pansapiens/blue-peaks/firmware/peaks2/modulations/lfo.cc

// Copyright 2013 Emilie Gillet, 2015 Tim Churches
//
// Author: Emilie Gillet (emilie.o.gillet@gmail.com)
// Modifications: Tim Churches (tim.churches@gmail.com)
// Modifications may be determined by examining the differences between the last commit
// by Emilie Gillet (pichenettes) and the HEAD commit at
// https://github.com/timchurches/Mutated-Mutables/tree/master/peaks
//
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
// See http://creativecommons.org/licenses/MIT/ for more information.
//
// -----------------------------------------------------------------------------
//
// LFO.

#include "peaks2/modulations/lfo.h"

#include <cstdio>

#include "stmlib/utils/dsp.h"
#include "stmlib/utils/random.h"

#include "peaks2/resources.h"

namespace peaks {

const uint16_t kSlopeBits = 12;
const uint32_t kSyncCounterMaxTime = 8 * 48000;

using namespace stmlib;

void Lfo::Init() {
  rate_ = 0;
  shape_ = LFO_SHAPE_SQUARE;
  parameter_ = 0;
  reset_phase_ = 0;
  sync_ = false;
  previous_parameter_ = 32767;
  sync_counter_ = kSyncCounterMaxTime;
  level_ = 32767;
  pattern_predictor_.Init();
}

const int16_t presets[7][2] = {
  { LFO_SHAPE_SINE, 0 },
  { LFO_SHAPE_TRIANGLE, 0 },
  { LFO_SHAPE_TRIANGLE, 32767 },
  { LFO_SHAPE_SQUARE, 0 },
  { LFO_SHAPE_STEPS, 0 },
  { LFO_SHAPE_NOISE, -32767 },
  { LFO_SHAPE_NOISE, 32767 },
};

void Lfo::set_shape_parameter_preset(uint16_t value) {
  value = (value >> 8) * 7 >> 8;
  set_shape(static_cast<LfoShape>(presets[value][0]));
  set_parameter(presets[value][1]);
}

void Lfo::Process(const GateFlags* gate_flags, int16_t* out, size_t size) {
  if (!sync_) {
    int32_t a = lut_lfo_increments[rate_ >> 8];
    int32_t b = lut_lfo_increments[(rate_ >> 8) + 1];
    phase_increment_ = a + (((b - a) >> 1) * (rate_ & 0xff) >> 7);
  }
  while (size--) {
    ++sync_counter_;
    GateFlags gate_flag = *gate_flags++;
    if (gate_flag & GATE_FLAG_RISING) {
      bool reset_phase = true;
      if (sync_) {
        if (sync_counter_ < kSyncCounterMaxTime) {
          uint32_t period = 0;
          if (gate_flag & GATE_FLAG_FROM_BUTTON) {
            period = sync_counter_;
          } else if (sync_counter_ < 1920) {
            period = (3 * period_ + sync_counter_) >> 2;
            reset_phase = false;
          } else {
            period = pattern_predictor_.Predict(sync_counter_);
          }
          if (period != period_) {
            period_ = period;
            phase_increment_ = 0xffffffff / period_;
          }
        }
        sync_counter_ = 0;
      }
      if (reset_phase) {
        phase_ = reset_phase_;
      }
    }
    phase_ += phase_increment_;
    int32_t sample = (this->*compute_sample_fn_table_[shape_])();
    *out++ = sample * level_ >> 15;
  }
}

int16_t Lfo::ComputeSampleSine() {
  uint32_t phase = phase_;
  int16_t sine = Interpolate1022(wav_sine, phase);
  int16_t sample;
  if (parameter_ > 0) {
    int32_t wf_balance = parameter_;
    int32_t wf_gain = 2048 + \
        (static_cast<int32_t>(parameter_) * (65535 - 2048) >> 15);
    int32_t original = sine;
    int32_t folded = Interpolate1022(
        wav_fold_sine, original * wf_gain + (1UL << 31));
    sample = original + ((folded - original) * wf_balance >> 15);
  } else {
    int32_t wf_balance = -parameter_;
    int32_t original = sine;
    phase += 1UL << 30;
    int32_t tri = phase < (1UL << 31) ? phase << 1 : ~(phase << 1);
    int32_t folded = Interpolate1022(wav_fold_power, tri);
    sample = original + ((folded - original) * wf_balance >> 15);
  }
  return sample;
}

int16_t Lfo::ComputeSampleTriangle() {
  if (parameter_ != previous_parameter_) {
    uint16_t slope_offset = parameter_ + 32768;
    if (slope_offset <= 1) {
      decay_factor_ = 32768 << kSlopeBits;
      attack_factor_ = 1 << (kSlopeBits - 1);
    } else {
      decay_factor_ = (32768 << kSlopeBits) / slope_offset;
      attack_factor_ = (32768 << kSlopeBits) / (65536 - slope_offset);
    }
    end_of_attack_ = (static_cast<uint32_t>(slope_offset) << 16);
    previous_parameter_ = parameter_;
  }

  uint32_t phase = phase_;
  uint32_t skewed_phase = phase;
  if (phase < end_of_attack_) {
    skewed_phase = (phase >> kSlopeBits) * decay_factor_;
  } else {
    skewed_phase = ((phase - end_of_attack_) >> kSlopeBits) * attack_factor_;
    skewed_phase += 1L << 31;
  }
  return skewed_phase < 1UL << 31
      ? -32768 + (skewed_phase >> 15)
      :  32767 - (skewed_phase >> 15);
}

int16_t Lfo::ComputeSampleSquare() {
  uint32_t threshold = static_cast<uint32_t>(parameter_ + 32768) << 16;
  if (threshold < (phase_increment_ << 1)) {
    threshold = phase_increment_ << 1;
  } else if (~threshold < (phase_increment_ << 1)) {
    threshold = ~(phase_increment_ << 1);
  }
  return phase_ < threshold ? 32767 : -32767;
}

int16_t Lfo::ComputeSampleSteps() {
  uint16_t quantization_levels = 2 + (((parameter_ + 32768) * 15) >> 16);
  uint16_t scale = 65535 / (quantization_levels - 1);
  uint32_t phase = phase_;
  uint32_t tri_phase = phase;
  uint32_t tri = tri_phase < (1UL << 31) ? tri_phase << 1 : ~(tri_phase << 1);
  return ((tri >> 16) * quantization_levels >> 16) * scale - 32768;
}

int16_t Lfo::ComputeSampleNoise() {
  uint32_t phase = phase_;
  if (phase < phase_increment_) {
    value_ = next_value_;
    next_value_ = Random::GetSample();
  }
  int16_t sample;
  int32_t linear_interpolation = value_ + \
      ((next_value_ - value_) * static_cast<int32_t>(phase >> 17) >> 15);
  if (parameter_ < 0) {
    int32_t balance = parameter_ + 32767;
    sample = value_ + ((linear_interpolation - value_) * balance >> 15);
  } else {
    int16_t raised_cosine = Interpolate824(lut_raised_cosine, phase) >> 1;
    int32_t smooth_interpolation = value_ + \
        ((next_value_ - value_) * raised_cosine >> 15);
    sample = linear_interpolation + \
        ((smooth_interpolation - linear_interpolation) * parameter_ >> 15);
  }
  return sample;
}

/* static */
Lfo::ComputeSampleFn Lfo::compute_sample_fn_table_[] = {
  &Lfo::ComputeSampleSine,
  &Lfo::ComputeSampleTriangle,
  &Lfo::ComputeSampleSquare,
  &Lfo::ComputeSampleSteps,
  &Lfo::ComputeSampleNoise
};

// Repeat for internally frequency-modulated LFO

void FmLfo::Init() {
  rate_ = 0;
  shape_ = LFO_SHAPE_SQUARE;
  parameter_ = 0;
  reset_phase_ = 0;
  previous_parameter_ = 32767;
  level_ = 32767;
  fm_rate_ = 0;
  fm_parameter_ = 0;
  fm_reset_phase_ = 0;
  fm_delta_ = 0 ;

}

void FmLfo::set_shape_parameter_preset(uint16_t value) {
  value = (value >> 8) * 7 >> 8;
  set_shape(static_cast<LfoShape>(presets[value][0]));
  set_parameter(presets[value][1]);
}

void FmLfo::Process(const GateFlags* gate_flags, int16_t* out, size_t size) {
  while (size--) {
    // internal FM oscillator first
    int32_t fm_a = lut_lfo_increments[fm_rate_ >> 8];
    int32_t fm_b = lut_lfo_increments[(fm_rate_ >> 8) + 1];
    fm_phase_increment_ = fm_a + (((fm_b - fm_a) >> 1) * (fm_rate_ & 0xff) >> 7);

    GateFlags gate_flag = *gate_flags++;
    if (gate_flag & GATE_FLAG_RISING) {
      bool fm_reset_phase = true;
      if (fm_reset_phase) {
        fm_phase_ = fm_reset_phase_;
      }
    }

    fm_phase_ += fm_phase_increment_;
    int32_t fm_sample = FmLfo::ComputeModulation();
    fm_delta_ = (fm_sample * fm_depth_) >> 18;
    // now actual LFO
    uint32_t unclipped_modulated_rate = rate_ + fm_delta_;
    if (unclipped_modulated_rate > 65535) {
      unclipped_modulated_rate = 65335 ;
    } else if (unclipped_modulated_rate <0) {
      unclipped_modulated_rate = 0 ;
    }
    uint16_t modulated_rate = static_cast<uint16_t>(unclipped_modulated_rate) ;
    int32_t a = lut_lfo_increments[modulated_rate >> 8];
    int32_t b = lut_lfo_increments[(modulated_rate >> 8) + 1];
    phase_increment_ = a + (((b - a) >> 1) * (modulated_rate & 0xff) >> 7);

    if (gate_flag & GATE_FLAG_RISING) {
      bool reset_phase = true;
      if (reset_phase) {
        phase_ = reset_phase_;
      }
    }
    phase_ += phase_increment_;
    int32_t sample = (this->*compute_sample_fn_table_[shape_])();
    *out++ = sample * level_ >> 15;
  }
}

int16_t FmLfo::ComputeSampleSine() {
  uint32_t phase = phase_;
  int16_t sine = Interpolate1022(wav_sine, phase);
  int16_t sample;
  if (parameter_ > 0) {
    int32_t wf_balance = parameter_;
    int32_t wf_gain = 2048 + \
        (static_cast<int32_t>(parameter_) * (65535 - 2048) >> 15);
    int32_t original = sine;
    int32_t folded = Interpolate1022(
        wav_fold_sine, original * wf_gain + (1UL << 31));
    sample = original + ((folded - original) * wf_balance >> 15);
  } else {
    int32_t wf_balance = -parameter_;
    int32_t original = sine;
    phase += 1UL << 30;
    int32_t tri = phase < (1UL << 31) ? phase << 1 : ~(phase << 1);
    int32_t folded = Interpolate1022(wav_fold_power, tri);
    sample = original + ((folded - original) * wf_balance >> 15);
  }
  return sample;
}

int16_t FmLfo::ComputeModulation() {
  uint32_t phase = fm_phase_;
  int16_t sine = Interpolate1022(wav_sine, phase);
  int16_t sample;
  if (!random_mod_) {
    int32_t wf_balance = fm_parameter_;
    int32_t wf_gain = 2048 + \
          (static_cast<int32_t>(fm_parameter_) * (65535 - 2048) >> 15);
    int32_t original = sine;
    int32_t folded = Interpolate1022(
          wav_fold_sine, original * wf_gain + (1UL << 31));
    sample = original + ((folded - original) * wf_balance >> 15);
  } else {
    if (phase < fm_phase_increment_) {
      fm_value_ = fm_next_value_;
      fm_next_value_ = Random::GetSample();
    }
    int32_t linear_interpolation = fm_value_ + \
        ((fm_next_value_ - fm_value_) * static_cast<int32_t>(phase >> 17) >> 15);
    int16_t raised_cosine = Interpolate824(lut_raised_cosine, phase) >> 1;
    int32_t smooth_interpolation = fm_value_ + \
          ((next_value_ - fm_value_) * raised_cosine >> 15);
    sample = linear_interpolation + \
          ((smooth_interpolation - linear_interpolation) * fm_parameter_ >> 15);
  }
  return sample;
}

int16_t FmLfo::ComputeSampleTriangle() {
  if (parameter_ != previous_parameter_) {
    uint16_t slope_offset = parameter_ + 32768;
    if (slope_offset <= 1) {
      decay_factor_ = 32768 << kSlopeBits;
      attack_factor_ = 1 << (kSlopeBits - 1);
    } else {
      decay_factor_ = (32768 << kSlopeBits) / slope_offset;
      attack_factor_ = (32768 << kSlopeBits) / (65536 - slope_offset);
    }
    end_of_attack_ = (static_cast<uint32_t>(slope_offset) << 16);
    previous_parameter_ = parameter_;
  }

  uint32_t phase = phase_;
  uint32_t skewed_phase = phase;
  if (phase < end_of_attack_) {
    skewed_phase = (phase >> kSlopeBits) * decay_factor_;
  } else {
    skewed_phase = ((phase - end_of_attack_) >> kSlopeBits) * attack_factor_;
    skewed_phase += 1L << 31;
  }
  return skewed_phase < 1UL << 31
      ? -32768 + (skewed_phase >> 15)
      :  32767 - (skewed_phase >> 15);
}

int16_t FmLfo::ComputeSampleSquare() {
  uint32_t threshold = static_cast<uint32_t>(parameter_ + 32768) << 16;
  if (threshold < (phase_increment_ << 1)) {
    threshold = phase_increment_ << 1;
  } else if (~threshold < (phase_increment_ << 1)) {
    threshold = ~(phase_increment_ << 1);
  }
  return phase_ < threshold ? 32767 : -32767;
}

int16_t FmLfo::ComputeSampleSteps() {
  uint16_t quantization_levels = 2 + (((parameter_ + 32768) * 15) >> 16);
  uint16_t scale = 65535 / (quantization_levels - 1);
  uint32_t phase = phase_;
  uint32_t tri_phase = phase;
  uint32_t tri = tri_phase < (1UL << 31) ? tri_phase << 1 : ~(tri_phase << 1);
  return ((tri >> 16) * quantization_levels >> 16) * scale - 32768;
}

int16_t FmLfo::ComputeSampleNoise() {
  uint32_t phase = phase_;
  if (phase < phase_increment_) {
    value_ = next_value_;
    next_value_ = Random::GetSample();
  }
  int16_t sample;
  int32_t linear_interpolation = value_ + \
      ((next_value_ - value_) * static_cast<int32_t>(phase >> 17) >> 15);
  if (parameter_ <= 0) {
    int32_t balance = parameter_ + 32767;
    sample = value_ + ((linear_interpolation - value_) * balance >> 15);
  } else {
    int16_t raised_cosine = Interpolate824(lut_raised_cosine, phase) >> 1;
    int32_t smooth_interpolation = value_ + \
        ((next_value_ - value_) * raised_cosine >> 15);
    sample = linear_interpolation + \
        ((smooth_interpolation - linear_interpolation) * parameter_ >> 15);
  }
  return sample;
}

/* static */
FmLfo::ComputeSampleFn FmLfo::compute_sample_fn_table_[] = {
  &FmLfo::ComputeSampleSine,
  &FmLfo::ComputeSampleTriangle,
  &FmLfo::ComputeSampleSquare,
  &FmLfo::ComputeSampleSteps,
  &FmLfo::ComputeSampleNoise
};

////////////////////////////////////////////////
// Repeat for internally waveshape-modulated LFO

void WsmLfo::Init() {
  rate_ = 0;
  shape_ = WSMLFO_SHAPE_SQUARE;
  parameter_ = 0;
  reset_phase_ = 0;
  previous_parameter_ = 32767;
  level_ = 32767;
  wsm_rate_ = 0;
  wsm_parameter_ = 0;
  wsm_reset_phase_ = 0;
  wsm_delta_ = 0 ;
}

const int16_t wsmlfo_presets[7][2] = {
  { WSMLFO_SHAPE_FOLDED_SINE, 0 },
  { WSMLFO_SHAPE_FOLDED_POWER_SINE, 0 },
  { WSMLFO_SHAPE_OVERDRIVEN_SINE, 0 },
  { WSMLFO_SHAPE_TRIANGLE, 0 },
  { WSMLFO_SHAPE_TRIANGLE, 32767 },
  { WSMLFO_SHAPE_SQUARE, 0 },
  { WSMLFO_SHAPE_NOISE, -32767 },
  // { WSMLFO_SHAPE_NOISE, 32767 },
} ;

void WsmLfo::set_shape_parameter_preset(uint16_t value) {
  value = (value >> 8) * 7 >> 8;
  set_shape(static_cast<WsmLfoShape>(presets[value][0]));
  set_parameter(presets[value][1]);
}

void WsmLfo::Process(const GateFlags* gate_flags, int16_t* out, size_t size) {
  while (size--) {
    // internal waveshape modulation oscillator first
    int32_t wsm_a = lut_lfo_increments[wsm_rate_ >> 8];
    int32_t wsm_b = lut_lfo_increments[(wsm_rate_ >> 8) + 1];
    wsm_phase_increment_ = wsm_a + (((wsm_b - wsm_a) >> 1) * (wsm_rate_ & 0xff) >> 7);
    GateFlags gate_flag = *gate_flags++;
    if (gate_flag & GATE_FLAG_RISING) {
      bool wsm_reset_phase = true;
      if (wsm_reset_phase) {
        wsm_phase_ = wsm_reset_phase_;
      }
    }
    wsm_phase_ += wsm_phase_increment_;
    int32_t wsm_sample = WsmLfo::ComputeModulation();
    wsm_delta_ = (wsm_sample * wsm_depth_) >> 16;
    parameter_ = wsm_delta_ ;
    // now actual LFO
    int32_t a = lut_lfo_increments[rate_ >> 8];
    int32_t b = lut_lfo_increments[(rate_ >> 8) + 1];
    phase_increment_ = a + (((b - a) >> 1) * (rate_ & 0xff) >> 7);
    if (gate_flag & GATE_FLAG_RISING) {
      bool reset_phase = true;
      if (reset_phase) {
        phase_ = reset_phase_;
      }
    }
    phase_ += phase_increment_;
    int32_t sample = (this->*compute_sample_fn_table_[shape_])();
    *out++ = sample;
  }
}

int16_t WsmLfo::ComputeSampleFoldedSine() {
  uint32_t phase = phase_;
  int16_t sine = Interpolate1022(wav_sine, phase);
  int16_t sample;
  int32_t wf_balance = (parameter_ + 32767) >> 1;
  int32_t wf_gain = 2048 + \
        (static_cast<int32_t>(parameter_) * (65535 - 2048) >> 15);
  int32_t original = sine;
  int32_t folded = Interpolate1022(
        wav_fold_sine, original * wf_gain + (1UL << 31));
  sample = original + ((folded - original) * wf_balance >> 15);
  return sample;
}

int16_t WsmLfo::ComputeSampleFoldedPowerSine() {
  uint32_t phase = phase_;
  int16_t sine = Interpolate1022(wav_sine, phase);
  int16_t sample;
  int32_t wf_balance = (parameter_ + 32767) >> 1;
  int32_t original = sine;
  phase += 1UL << 30;
  int32_t tri = phase < (1UL << 31) ? phase << 1 : ~(phase << 1);
  int32_t folded = Interpolate1022(wav_fold_power, tri);
  sample = original + ((folded - original) * wf_balance >> 15);
  return sample ;
}

int16_t WsmLfo::ComputeSampleOverdrivenSine() {
  uint32_t phase = phase_;
  int16_t sine = Interpolate1022(wav_sine, phase);
  int16_t sample;
  int32_t wf_balance = (parameter_ + 32767) >> 1;
  int32_t wf_gain = 2048 + \
        (static_cast<int32_t>(parameter_) * (65535 - 2048) >> 15);
  int32_t original = sine;
  int32_t folded = Interpolate1022(
        wav_overdrive, original * wf_gain + (1UL << 31));
  sample = original + ((folded - original) * wf_balance >> 15);
  return sample;
}

int16_t WsmLfo::ComputeModulation() {
  uint32_t phase = wsm_phase_;
  int16_t sample;
  if (!random_mod_) {
    int16_t sine = Interpolate1022(wav_sine, phase);
    int32_t wf_balance = wsm_parameter_;
    int32_t wf_gain = 2048 + \
        (static_cast<int32_t>(wsm_parameter_) * (65535 - 2048) >> 15);
    int32_t original = sine;
    int32_t folded = Interpolate1022(
        wav_fold_sine, original * wf_gain + (1UL << 31));
    sample = original + ((folded - original) * wf_balance >> 15);
  } else {
    if (phase < wsm_phase_increment_) {
      wsm_value_ = wsm_next_value_;
      wsm_next_value_ = Random::GetSample();
    }
    int32_t linear_interpolation = wsm_value_ + \
        ((wsm_next_value_ - wsm_value_) * static_cast<int32_t>(phase >> 17) >> 15);
    int16_t raised_cosine = Interpolate824(lut_raised_cosine, phase) >> 1;
    int32_t smooth_interpolation = wsm_value_ + \
          ((wsm_next_value_ - wsm_value_) * raised_cosine >> 15);
    sample = linear_interpolation + \
          ((smooth_interpolation - linear_interpolation) * wsm_parameter_ >> 15);
  }
  return sample;
}

int16_t WsmLfo::ComputeSampleTriangle() {
  if (parameter_ != previous_parameter_) {
    uint16_t slope_offset = parameter_ + 32768;
    if (slope_offset <= 1) {
      decay_factor_ = 32768 << kSlopeBits;
      attack_factor_ = 1 << (kSlopeBits - 1);
    } else {
      decay_factor_ = (32768 << kSlopeBits) / slope_offset;
      attack_factor_ = (32768 << kSlopeBits) / (65536 - slope_offset);
    }
    end_of_attack_ = (static_cast<uint32_t>(slope_offset) << 16);
    previous_parameter_ = parameter_;
  }

  uint32_t phase = phase_;
  uint32_t skewed_phase = phase;
  if (phase < end_of_attack_) {
    skewed_phase = (phase >> kSlopeBits) * decay_factor_;
  } else {
    skewed_phase = ((phase - end_of_attack_) >> kSlopeBits) * attack_factor_;
    skewed_phase += 1L << 31;
  }
  return skewed_phase < 1UL << 31
      ? -32768 + (skewed_phase >> 15)
      :  32767 - (skewed_phase >> 15);
}

int16_t WsmLfo::ComputeSampleSquare() {
  uint32_t threshold = static_cast<uint32_t>(parameter_ + 32768) << 16;
  if (threshold < (phase_increment_ << 1)) {
    threshold = phase_increment_ << 1;
  } else if (~threshold < (phase_increment_ << 1)) {
    threshold = ~(phase_increment_ << 1);
  }
  return phase_ < threshold ? 32767 : -32767;
}

int16_t WsmLfo::ComputeSampleNoise() {
  uint32_t phase = phase_;
  if (phase < phase_increment_) {
    value_ = next_value_;
    next_value_ = Random::GetSample();
  }
  int16_t sample;
  int32_t linear_interpolation = value_ + \
      ((next_value_ - value_) * static_cast<int32_t>(phase >> 17) >> 15);
  if (parameter_ <= 0) {
    int32_t balance = parameter_ + 32767;
    sample = value_ + ((linear_interpolation - value_) * balance >> 15);
  } else {
    int16_t raised_cosine = Interpolate824(lut_raised_cosine, phase) >> 1;
    int32_t smooth_interpolation = value_ + \
        ((next_value_ - value_) * raised_cosine >> 15);
    sample = linear_interpolation + \
        ((smooth_interpolation - linear_interpolation) * parameter_ >> 15);
  }
  return sample;
}

/* static */
WsmLfo::ComputeSampleFn WsmLfo::compute_sample_fn_table_[] = {
  &WsmLfo::ComputeSampleFoldedSine,
  &WsmLfo::ComputeSampleFoldedPowerSine,
  &WsmLfo::ComputeSampleOverdrivenSine,
  &WsmLfo::ComputeSampleTriangle,
  &WsmLfo::ComputeSampleSquare,
  &WsmLfo::ComputeSampleNoise
};

///////////////////////////////////////////
// Repeat for audio-frequency PLL oscillator

void Plo::Init() {
  rate_ = 0;
  shape_ = WSMLFO_SHAPE_SQUARE;
  parameter_ = 0;
  // reset_phase_ = 0;
  sync_ = true;
  previous_parameter_ = 32767;
  level_ = 32767;
  wsm_rate_ = 0;
  wsm_parameter_ = 0;
  // wsm_reset_phase_ = 0;
  // wsm_delta_ = 0 ;

  sync_counter_ = kSyncCounterMaxTime;
  pattern_predictor_.Init();

  pitch_multiplier_ = 0;
}

void Plo::set_shape_parameter_preset(uint16_t value) {
  value = (value >> 8) * 7 >> 8;
  set_shape(static_cast<WsmLfoShape>(presets[value][0]));
  set_parameter(presets[value][1]);
}

void Plo::set_pitch_coefficient(uint16_t value) {
  pitch_multiplier_ = static_cast<int8_t>(static_cast<int16_t>(-32767 + value) >> 13);
}

void Plo::Process(const GateFlags* gate_flags, int16_t* out, size_t size) {
  while (size--) {
    GateFlags gate_flag = *gate_flags++;

    // internal waveshape modulation oscillator first
    if (wsm_depth_) {
      int32_t wsm_a = lut_lfo_increments[wsm_rate_ >> 8];
      int32_t wsm_b = lut_lfo_increments[(wsm_rate_ >> 8) + 1];
      wsm_phase_increment_ = wsm_a + (((wsm_b - wsm_a) >> 1) * (wsm_rate_ & 0xff) >> 7);
      wsm_phase_ += wsm_phase_increment_;
      int32_t wsm_sample = Plo::ComputeModulationSine();
      parameter_ = (wsm_sample * wsm_depth_) >> 16;
    }

    ++sync_counter_;
    if (gate_flag & GATE_FLAG_RISING) {
        if (sync_counter_ < kSyncCounterMaxTime) {
          uint32_t period = 0;
          if (sync_counter_ < 1920) {
            period = (3 * period_ + sync_counter_) >> 2;
          } else {
            period = pattern_predictor_.Predict(sync_counter_);
          }
          if (period != period_) {
            period_ = period;
            phase_increment_ = 0xffffffff / period;
            phase_increment_ = pitch_multiplier_ < 0 ?
                                phase_increment_ >> -pitch_multiplier_ :
                                phase_increment_ << pitch_multiplier_ ;
          }
        }
        sync_counter_ = 0;
    }
    phase_ += phase_increment_;
    // int32_t sample = (this->*compute_sample_fn_table_[shape_])();
    // output_buffer->Overwrite(sample);
    *out++ = (this->*compute_sample_fn_table_[shape_])();
  }
}

int16_t Plo::ComputeSampleFoldedSine() {
  uint32_t phase = phase_;
  int16_t sine = Interpolate1022(wav_sine, phase);
  int16_t sample;
  int32_t wf_balance = (parameter_ + 32767) >> 1;
  int32_t wf_gain = 2048 + \
        (static_cast<int32_t>(parameter_) * (65535 - 2048) >> 15);
  int32_t original = sine;
  int32_t folded = Interpolate1022(
        wav_fold_sine, original * wf_gain + (1UL << 31));
  sample = original + ((folded - original) * wf_balance >> 15);
  return sample;
}

int16_t Plo::ComputeSampleFoldedPowerSine() {
  uint32_t phase = phase_;
  int16_t sine = Interpolate1022(wav_sine, phase);
  int16_t sample;
  int32_t wf_balance = (parameter_ + 32767) >> 1;
  int32_t original = sine;
  phase += 1UL << 30;
  int32_t tri = phase < (1UL << 31) ? phase << 1 : ~(phase << 1);
  int32_t folded = Interpolate1022(wav_fold_power, tri);
  sample = original + ((folded - original) * wf_balance >> 15);
  return sample ;
}

int16_t Plo::ComputeSampleOverdrivenSine() {
  uint32_t phase = phase_;
  int16_t sine = Interpolate1022(wav_sine, phase);
  int16_t sample;
  int32_t wf_balance = (parameter_ + 32767) >> 1;
  int32_t wf_gain = 2048 + \
        (static_cast<int32_t>(parameter_) * (65535 - 2048) >> 15);
  int32_t original = sine;
  int32_t folded = Interpolate1022(
        wav_overdrive, original * wf_gain + (1UL << 31));
  sample = original + ((folded - original) * wf_balance >> 15);
  return sample;
}

int16_t Plo::ComputeModulationSine() {
  uint32_t phase = wsm_phase_;
  int16_t sine = Interpolate1022(wav_sine, phase);
  return sine ;
}

int16_t Plo::ComputeSampleTriangle() {
  if (parameter_ != previous_parameter_) {
    uint16_t slope_offset = parameter_ + 32768;
    if (slope_offset <= 1) {
      decay_factor_ = 32768 << kSlopeBits;
      attack_factor_ = 1 << (kSlopeBits - 1);
    } else {
      decay_factor_ = (32768 << kSlopeBits) / slope_offset;
      attack_factor_ = (32768 << kSlopeBits) / (65536 - slope_offset);
    }
    end_of_attack_ = (static_cast<uint32_t>(slope_offset) << 16);
    previous_parameter_ = parameter_;
  }

  uint32_t phase = phase_;
  uint32_t skewed_phase = phase;
  if (phase < end_of_attack_) {
    skewed_phase = (phase >> kSlopeBits) * decay_factor_;
  } else {
    skewed_phase = ((phase - end_of_attack_) >> kSlopeBits) * attack_factor_;
    skewed_phase += 1L << 31;
  }
  return skewed_phase < 1UL << 31
      ? -32768 + (skewed_phase >> 15)
      :  32767 - (skewed_phase >> 15);
}

int16_t Plo::ComputeSampleSquare() {
  uint32_t threshold = static_cast<uint32_t>(parameter_ + 32768) << 16;
  if (threshold < (phase_increment_ << 1)) {
    threshold = phase_increment_ << 1;
  } else if (~threshold < (phase_increment_ << 1)) {
    threshold = ~(phase_increment_ << 1);
  }
  return phase_ < threshold ? 32767 : -32767;
}

int16_t Plo::ComputeSampleNoise() {
  uint32_t phase = phase_;
  if (phase < phase_increment_) {
    value_ = next_value_;
    next_value_ = Random::GetSample();
  }
  int16_t sample;
  int32_t linear_interpolation = value_ + \
      ((next_value_ - value_) * static_cast<int32_t>(phase >> 17) >> 15);
  if (parameter_ < 0) {
    int32_t balance = parameter_ + 32767;
    sample = value_ + ((linear_interpolation - value_) * balance >> 15);
  } else {
    int16_t raised_cosine = Interpolate824(lut_raised_cosine, phase) >> 1;
    int32_t smooth_interpolation = value_ + \
        ((next_value_ - value_) * raised_cosine >> 15);
    sample = linear_interpolation + \
        ((smooth_interpolation - linear_interpolation) * parameter_ >> 15);
  }
  return sample;
}

/* static */
Plo::ComputeSampleFn Plo::compute_sample_fn_table_[] = {
  &Plo::ComputeSampleFoldedSine,
  &Plo::ComputeSampleFoldedPowerSine,
  &Plo::ComputeSampleOverdrivenSine,
  &Plo::ComputeSampleTriangle,
  &Plo::ComputeSampleSquare,
  &Plo::ComputeSampleNoise
};

}  // namespace peaks
