pansapiens/blue-peaks/firmware/peaks2/modulations/multistage_envelope.h

// Copyright 2013 Emilie Gillet, 2015 Tim Churches
//
// Author: Emilie Gillet (emilie.o.gillet@gmail.com)
// Modifications: Tim Churches (tim.churches@gmail.com)
// Modifications may be determined by examining the differences between the last commit
// by Emilie Gillet (pichenettes) and the HEAD commit at
// https://github.com/timchurches/Mutated-Mutables/tree/master/peaks
//
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
// See http://creativecommons.org/licenses/MIT/ for more information.
//
// -----------------------------------------------------------------------------
//
// Multistage envelope.

#ifndef PEAKS_MODULATIONS_MULTISTAGE_ENVELOPE_H_
#define PEAKS_MODULATIONS_MULTISTAGE_ENVELOPE_H_

#include "stmlib/stmlib.h"
#include "stmlib/utils/ring_buffer.h"

#include "peaks2/gate_processor.h"

namespace peaks {

enum EnvelopeShape {
  ENV_SHAPE_LINEAR,
  ENV_SHAPE_EXPONENTIAL,
  ENV_SHAPE_QUARTIC
};

const uint16_t kMaxNumSegments = 8;

class MultistageEnvelope {
 public:
  MultistageEnvelope() { }
  ~MultistageEnvelope() { }

  void Init();
  void Process(const GateFlags* gate_flags, int16_t* out, size_t size);

  void Configure(uint16_t* parameter, ControlMode control_mode) {
    if (control_mode == CONTROL_MODE_HALF) {
      set_ad(parameter[0], parameter[1]);
    } else {
      set_adsr(parameter[0], parameter[1], parameter[2] >> 1, parameter[3]);
    }
    if (segment_ > num_segments_) {
      segment_ = 0;
      phase_ = 0;
      value_ = 0;
    }
  }

  inline void set_time(uint16_t segment, uint16_t time) {
    time_[segment] = time;
  }

  inline void set_level(uint16_t segment, int16_t level) {
    level_[segment] = level;
  }

  inline void set_num_segments(uint16_t num_segments) {
    num_segments_ = num_segments;
  }

  inline void set_sustain_point(uint16_t sustain_point) {
    sustain_point_ = sustain_point;
  }

  inline void set_adsr(
      uint16_t attack,
      uint16_t decay,
      uint16_t sustain,
      uint16_t release) {
    num_segments_ = 3;
    sustain_point_ = 2;

    level_[0] = 0;
    level_[1] = 32767;
    level_[2] = sustain;
    level_[3] = 0;

    time_[0] = attack;
    time_[1] = decay;
    time_[2] = release;

    shape_[0] = ENV_SHAPE_QUARTIC;
    shape_[1] = ENV_SHAPE_EXPONENTIAL;
    shape_[2] = ENV_SHAPE_EXPONENTIAL;

    loop_start_ = loop_end_ = 0;
  }

  inline void set_ad(uint16_t attack, uint16_t decay) {
    num_segments_ = 2;
    sustain_point_ = 0;

    level_[0] = 0;
    level_[1] = 32767;
    level_[2] = 0;

    time_[0] = attack;
    time_[1] = decay;

    shape_[0] = ENV_SHAPE_QUARTIC;
    shape_[1] = ENV_SHAPE_EXPONENTIAL;

    loop_start_ = loop_end_ = 0;
  }

  inline void set_hard_reset(bool hard_reset) {
    hard_reset_ = hard_reset;
  }

 private:
  int16_t level_[kMaxNumSegments];
  uint16_t time_[kMaxNumSegments];
  EnvelopeShape shape_[kMaxNumSegments];

  int16_t segment_;
  int16_t start_value_;
  int16_t value_;

  uint32_t phase_;
  uint32_t phase_increment_;

  uint16_t num_segments_;
  uint16_t sustain_point_;
  uint16_t loop_start_;
  uint16_t loop_end_;

  bool hard_reset_;

  DISALLOW_COPY_AND_ASSIGN(MultistageEnvelope);
};

// Just copy the class and adjust it rather than trying to subclass it...
class DualAttackEnvelope {
 public:
  DualAttackEnvelope() { }
  ~DualAttackEnvelope() { }

  void Init();
  void Process(const GateFlags* gate_flags, int16_t* out, size_t size);

  void Configure(uint16_t* parameter, ControlMode control_mode) {
    if (control_mode == CONTROL_MODE_HALF) {
      set_ad(parameter[0], parameter[1]);
    } else {
      set_adsar(parameter[0], parameter[1], parameter[2] >> 1, parameter[3]);
    }
    if (segment_ > num_segments_) {
      segment_ = 0;
      phase_ = 0;
      value_ = 0;
    }
  }

  inline void set_time(uint16_t segment, uint16_t time) {
    time_[segment] = time;
  }

  inline void set_level(uint16_t segment, int16_t level) {
    level_[segment] = level;
  }

  inline void set_num_segments(uint16_t num_segments) {
    num_segments_ = num_segments;
  }

  inline void set_sustain_point(uint16_t sustain_point) {
    sustain_point_ = sustain_point;
  }

  inline void set_ad(uint16_t attack, uint16_t decay) {
    num_segments_ = 2;
    sustain_point_ = 0;

    level_[0] = 0;
    level_[1] = 32767;
    level_[2] = 0;

    time_[0] = attack;
    time_[1] = decay;

    shape_[0] = ENV_SHAPE_LINEAR;
    shape_[1] = ENV_SHAPE_LINEAR;

    loop_start_ = loop_end_ = 0;
  }

  inline void set_adsar(
      uint16_t attack,
      uint16_t decay,
      uint16_t sustain,
      uint16_t release) {
    num_segments_ = 4;
    sustain_point_ = 2;

    level_[0] = 0;
    level_[1] = 32767;
    level_[2] = sustain;
    level_[3] = 32767;
    level_[4] = 0;

    time_[0] = attack;
    time_[1] = decay;
    time_[2] = attack;
    time_[3] = release;

    shape_[0] = ENV_SHAPE_QUARTIC;
    shape_[1] = ENV_SHAPE_EXPONENTIAL;
    shape_[2] = ENV_SHAPE_QUARTIC;
    shape_[3] = ENV_SHAPE_EXPONENTIAL;

    loop_start_ = loop_end_ = 0;
  }

  inline void set_hard_reset(bool hard_reset) {
    hard_reset_ = hard_reset;
  }

 private:
  int16_t level_[kMaxNumSegments];
  uint16_t time_[kMaxNumSegments];
  EnvelopeShape shape_[kMaxNumSegments];

  int16_t segment_;
  int16_t start_value_;
  int16_t value_;

  uint32_t phase_;
  uint32_t phase_increment_;

  uint16_t num_segments_;
  uint16_t sustain_point_;
  uint16_t loop_start_;
  uint16_t loop_end_;

  bool hard_reset_;

  DISALLOW_COPY_AND_ASSIGN(DualAttackEnvelope);
};

// And copy the class again...
class RepeatingAttackEnvelope {
 public:
  RepeatingAttackEnvelope() { }
  ~RepeatingAttackEnvelope() { }

  void Init();
  void Process(const GateFlags* gate_flags, int16_t* out, size_t size);

  void Configure(uint16_t* parameter, ControlMode control_mode) {
    if (control_mode == CONTROL_MODE_HALF) {
      set_ad_loop(parameter[0], parameter[1]);
    } else {
      set_adr_loop(parameter[0], parameter[1], parameter[2] >> 1, parameter[3]);
    }
    if (segment_ > num_segments_) {
      segment_ = 0;
      phase_ = 0;
      value_ = 0;
    }
  }

  inline void set_time(uint16_t segment, uint16_t time) {
    time_[segment] = time;
  }

  inline void set_level(uint16_t segment, int16_t level) {
    level_[segment] = level;
  }

  inline void set_num_segments(uint16_t num_segments) {
    num_segments_ = num_segments;
  }

  inline void set_sustain_point(uint16_t sustain_point) {
    sustain_point_ = sustain_point;
  }

  inline void set_ad_loop(uint16_t attack, uint16_t decay) {
    num_segments_ = 2;
    sustain_point_ = 0;

    level_[0] = 0;
    level_[1] = 32767;
    level_[2] = 0;

    time_[0] = attack;
    time_[1] = decay;

    shape_[0] = ENV_SHAPE_QUARTIC;
    shape_[1] = ENV_SHAPE_QUARTIC;

    loop_start_ = 0;
    loop_end_ = 2;
  }

  inline void set_adr_loop(
      uint16_t attack,
      uint16_t decay,
      uint16_t sustain,
      uint16_t release) {
    num_segments_ = 3;
    sustain_point_ = 0;

    level_[0] = 0;
    level_[1] = 32767;
    level_[2] = sustain;
    level_[3] = 0;

    time_[0] = attack;
    time_[1] = decay;
    time_[2] = release;

    shape_[0] = ENV_SHAPE_QUARTIC;
    shape_[1] = ENV_SHAPE_QUARTIC;
    shape_[2] = ENV_SHAPE_EXPONENTIAL;

    loop_start_ = 0;
    loop_end_ = 2; // was 3
  }

  inline void set_hard_reset(bool hard_reset) {
    hard_reset_ = hard_reset;
  }

 private:
  int16_t level_[kMaxNumSegments];
  uint16_t time_[kMaxNumSegments];
  EnvelopeShape shape_[kMaxNumSegments];

  int16_t segment_;
  int16_t start_value_;
  int16_t value_;

  uint32_t phase_;
  uint32_t phase_increment_;

  uint16_t num_segments_;
  uint16_t sustain_point_;
  uint16_t loop_start_;
  uint16_t loop_end_;

  bool hard_reset_;

  DISALLOW_COPY_AND_ASSIGN(RepeatingAttackEnvelope);
};


// And copy the class again...
class LoopingEnvelope {
 public:
  LoopingEnvelope() { }
  ~LoopingEnvelope() { }

  void Init();
  void Process(const GateFlags* gate_flags, int16_t* out, size_t size);

  void Configure(uint16_t* parameter, ControlMode control_mode) {
    if (control_mode == CONTROL_MODE_HALF) {
      set_ad_loop(parameter[0], parameter[1]);
    } else {
      set_adr_loop(parameter[0], parameter[1], parameter[2] >> 1, parameter[3]);
    }
    if (segment_ > num_segments_) {
      segment_ = 0;
      phase_ = 0;
      value_ = 0;
    }
  }

  inline void set_time(uint16_t segment, uint16_t time) {
    time_[segment] = time;
  }

  inline void set_level(uint16_t segment, int16_t level) {
    level_[segment] = level;
  }

  inline void set_num_segments(uint16_t num_segments) {
    num_segments_ = num_segments;
  }

  inline void set_sustain_point(uint16_t sustain_point) {
    sustain_point_ = sustain_point;
  }

  inline void set_ad_loop(uint16_t attack, uint16_t decay) {
    num_segments_ = 2;
    sustain_point_ = 0;

    level_[0] = 0;
    level_[1] = 32767;
    level_[2] = 0;

    time_[0] = attack;
    time_[1] = decay;

    shape_[0] = ENV_SHAPE_QUARTIC;
    shape_[1] = ENV_SHAPE_QUARTIC;

    loop_start_ = 0;
    loop_end_ = 2;
  }

  inline void set_adr_loop(
      uint16_t attack,
      uint16_t decay,
      uint16_t sustain,
      uint16_t release) {
    num_segments_ = 3;
    sustain_point_ = 0;

    level_[0] = 0;
    level_[1] = 32767;
    level_[2] = sustain;
    level_[3] = 0;

    time_[0] = attack;
    time_[1] = decay;
    time_[2] = release;

    shape_[0] = ENV_SHAPE_QUARTIC;
    shape_[1] = ENV_SHAPE_QUARTIC;
    shape_[2] = ENV_SHAPE_QUARTIC;

    loop_start_ = 0;
    loop_end_ = 3;
  }

  inline void set_hard_reset(bool hard_reset) {
    hard_reset_ = hard_reset;
  }

 private:
  int16_t level_[kMaxNumSegments];
  uint16_t time_[kMaxNumSegments];
  EnvelopeShape shape_[kMaxNumSegments];

  int16_t segment_;
  int16_t start_value_;
  int16_t value_;

  uint32_t phase_;
  uint32_t phase_increment_;

  uint16_t num_segments_;
  uint16_t sustain_point_;
  uint16_t loop_start_;
  uint16_t loop_end_;

  bool hard_reset_;

  DISALLOW_COPY_AND_ASSIGN(LoopingEnvelope);
};

// randomised AD envelope class
class RandomisedEnvelope {
 public:
  RandomisedEnvelope() { }
  ~RandomisedEnvelope() { }

  void Init();
  void Process(const GateFlags* gate_flags, int16_t* out, size_t size);

  void Configure(uint16_t* parameter, ControlMode control_mode) {
    if (control_mode == CONTROL_MODE_HALF) {
      set_rad_half(parameter[0], parameter[1]);
    } else {
      set_rad(parameter[0], parameter[1], parameter[2], parameter[3]);
    }
    if (segment_ > num_segments_) {
      segment_ = 0;
      phase_ = 0;
      value_ = 0;
    }
  }

  inline void set_time(uint16_t segment, uint16_t time) {
    time_[segment] = time;
  }

  inline void set_level(uint16_t segment, int16_t level) {
    level_[segment] = level;
  }

  inline void set_num_segments(uint16_t num_segments) {
    num_segments_ = num_segments;
  }

  inline void set_sustain_point(uint16_t sustain_point) {
    sustain_point_ = sustain_point;
  }

  inline void set_rad(uint16_t attack,
                      uint16_t decay,
                      uint16_t level_randomness,
                      uint16_t decay_randomness) {
    num_segments_ = 2;
    sustain_point_ = 0;

    level_randomness_ = level_randomness;
    decay_randomness_ = decay_randomness;

    base_level_[0] = 0;
    base_level_[1] = 32767;
    base_level_[2] = 0;

    level_[0] = 0;
    level_[1] = 32767;
    level_[2] = 0;

    base_time_[0] = attack;
    base_time_[1] = decay;

    time_[0] = attack;
    time_[1] = decay;

    shape_[0] = ENV_SHAPE_QUARTIC;
    shape_[1] = ENV_SHAPE_EXPONENTIAL;

    loop_start_ = loop_end_ = 0;
  }

  inline void set_rad_half(uint16_t attack, uint16_t decay) {
    num_segments_ = 2;
    sustain_point_ = 0;

    base_level_[0] = 0;
    base_level_[1] = 32767;
    base_level_[2] = 0;

    level_[0] = 0;
    level_[1] = 32767;
    level_[2] = 0;

    base_time_[0] = attack;
    base_time_[1] = decay;

    time_[0] = attack;
    time_[1] = decay;

    shape_[0] = ENV_SHAPE_QUARTIC;
    shape_[1] = ENV_SHAPE_EXPONENTIAL;

    loop_start_ = 0;
    loop_end_ = 0;
  }

  inline void set_hard_reset(bool hard_reset) {
    hard_reset_ = hard_reset;
  }

 private:
  int16_t level_[kMaxNumSegments];
  int16_t base_level_[kMaxNumSegments];

  uint16_t base_time_[kMaxNumSegments];
  uint16_t time_[kMaxNumSegments];
  EnvelopeShape shape_[kMaxNumSegments];

  int16_t segment_;
  int16_t start_value_;
  int16_t value_;

  uint32_t phase_;
  uint32_t phase_increment_;

  uint16_t num_segments_;
  uint16_t sustain_point_;
  uint16_t loop_start_;
  uint16_t loop_end_;

  bool hard_reset_;

  uint16_t level_randomness_ ;
  uint16_t decay_randomness_ ;

  DISALLOW_COPY_AND_ASSIGN(RandomisedEnvelope);
};


}  // namespace peaks

#endif  // PEAKS_MODULATIONS_MULTISTAGE_ENVELOPE_H_
