pansapiens/blue-peaks/firmware/peaks2/processors.h

// Copyright 2013 Emilie Gillet, 2015 Tim Churches
//
// Author: Emilie Gillet (emilie.o.gillet@gmail.com)
// Modifications: Tim Churches (tim.churches@gmail.com)
// Modifications may be determined by examining the differences between the last commit
// by Emilie Gillet (pichenettes) and the HEAD commit at
// https://github.com/timchurches/Mutated-Mutables/tree/master/peaks
//
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
// See http://creativecommons.org/licenses/MIT/ for more information.
//
// -----------------------------------------------------------------------------
//
// This is the common entry points for all types of modulation sources!

#ifndef PEAKS_PROCESSORS_H_
#define PEAKS_PROCESSORS_H_

#include "stmlib/stmlib.h"

#include <algorithm>

#include "peaks2/drums/bass_drum.h"
#include "peaks2/drums/fm_drum.h"
#include "peaks2/drums/snare_drum.h"
#include "peaks2/drums/high_hat.h"
#include "peaks2/modulations/bouncing_ball.h"
#include "peaks2/modulations/lfo.h"
#include "peaks2/modulations/mini_sequencer.h"
#include "peaks2/modulations/turing_machine.h"
#include "peaks2/modulations/multistage_envelope.h"
#ifdef NUMBER_STATION
#include "peaks2/number_station/number_station.h"
#endif
#include "peaks2/pulse_processor/pulse_shaper.h"
#include "peaks2/pulse_processor/pulse_randomizer.h"
#include "peaks2/bytebeats/bytebeats.h"

#include "peaks2/gate_processor.h"

namespace peaks {

enum ProcessorFunction {
  PROCESSOR_FUNCTION_ENVELOPE,
  PROCESSOR_FUNCTION_LFO,
  PROCESSOR_FUNCTION_TAP_LFO,
  PROCESSOR_FUNCTION_BASS_DRUM,
  PROCESSOR_FUNCTION_SNARE_DRUM,
  PROCESSOR_FUNCTION_HIGH_HAT,
  PROCESSOR_FUNCTION_FM_DRUM,
  PROCESSOR_FUNCTION_PULSE_SHAPER,
  PROCESSOR_FUNCTION_PULSE_RANDOMIZER,
  PROCESSOR_FUNCTION_MINI_SEQUENCER,
  PROCESSOR_FUNCTION_BYTEBEATS,
  #ifdef NUMBER_STATION
  PROCESSOR_FUNCTION_NUMBER_STATION,
  #endif
  PROCESSOR_FUNCTION_DUAL_ATTACK_ENVELOPE,
  PROCESSOR_FUNCTION_REPEATING_ATTACK_ENVELOPE,
  PROCESSOR_FUNCTION_LOOPING_ENVELOPE,
  PROCESSOR_FUNCTION_RANDOMISED_ENVELOPE,
  PROCESSOR_FUNCTION_BOUNCING_BALL,
  PROCESSOR_FUNCTION_RANDOMISED_BASS_DRUM,
  PROCESSOR_FUNCTION_RANDOMISED_SNARE_DRUM,
  PROCESSOR_FUNCTION_TURING_MACHINE,
  PROCESSOR_FUNCTION_MOD_SEQUENCER,
  PROCESSOR_FUNCTION_FMLFO,
  PROCESSOR_FUNCTION_RFMLFO,
  PROCESSOR_FUNCTION_WSMLFO,
  PROCESSOR_FUNCTION_RWSMLFO,
  PROCESSOR_FUNCTION_PLO,
  PROCESSOR_FUNCTION_LAST
};

#define DECLARE_PROCESSOR(ClassName, variable) \
  void ClassName ## Init() { \
    variable.Init(); \
  } \
  void ClassName ## Process(const GateFlags* gate_flags, int16_t* out, size_t size) { \
    variable.Process(gate_flags, out, size); \
  } \
  void ClassName ## Configure(uint16_t* p, ControlMode control_mode) { \
    variable.Configure(p, control_mode); \
  } \
  ClassName variable;

class Processors {
 public:
  Processors() { }
  ~Processors() { }

  void Init(uint8_t index);

  typedef void (Processors::*InitFn)();
  typedef void (Processors::*ProcessFn)(const GateFlags*, int16_t*, size_t);
  typedef void (Processors::*ConfigureFn)(uint16_t*, ControlMode);

  struct ProcessorCallbacks {
    InitFn init_fn;
    ProcessFn process_fn;
    ConfigureFn configure_fn;
  };

  inline void set_control_mode(ControlMode control_mode) {
    control_mode_ = control_mode;
    Configure();
  }

  inline void set_parameter(uint8_t index, uint16_t parameter) {
    parameter_[index] = parameter;
    Configure();
  }

  inline void CopyParameters(uint16_t* parameters, uint16_t size) {
    std::copy(&parameters[0], &parameters[size], &parameter_[0]);
  }

  inline void set_function(ProcessorFunction function) {
    function_ = function;
    lfo_.set_sync(function == PROCESSOR_FUNCTION_TAP_LFO);
    fmlfo_.set_mod_type(function == PROCESSOR_FUNCTION_RFMLFO);
    wsmlfo_.set_mod_type(function == PROCESSOR_FUNCTION_RWSMLFO);
    plo_.set_sync(function == PROCESSOR_FUNCTION_PLO);
    callbacks_ = callbacks_table_[function];
    if (function != PROCESSOR_FUNCTION_TAP_LFO and
        function != PROCESSOR_FUNCTION_PLO) {
      (this->*callbacks_.init_fn)();
    }
    Configure();
  }

  inline ProcessorFunction function() const { return function_; }

  inline void Process(const GateFlags* gate_flags, int16_t* output, size_t size) {
    (this->*callbacks_.process_fn)(gate_flags, output, size);
  }

#ifdef NUMBER_STATION
  inline const NumberStation& number_station() const { return number_station_; }
#endif

 private:
  void Configure() {
    (this->*callbacks_.configure_fn)(&parameter_[0], control_mode_);
  }

  ControlMode control_mode_;
  ProcessorFunction function_;
  uint16_t parameter_[4];

  ProcessorCallbacks callbacks_;
  static const ProcessorCallbacks callbacks_table_[PROCESSOR_FUNCTION_LAST];

  DECLARE_PROCESSOR(MultistageEnvelope, envelope_);
  DECLARE_PROCESSOR(Lfo, lfo_);
  DECLARE_PROCESSOR(BassDrum, bass_drum_);
  DECLARE_PROCESSOR(SnareDrum, snare_drum_);
  DECLARE_PROCESSOR(HighHat, high_hat_);
  DECLARE_PROCESSOR(FmDrum, fm_drum_);
  DECLARE_PROCESSOR(PulseShaper, pulse_shaper_);
  DECLARE_PROCESSOR(PulseRandomizer, pulse_randomizer_);
  DECLARE_PROCESSOR(BouncingBall, bouncing_ball_);
  DECLARE_PROCESSOR(MiniSequencer, mini_sequencer_);
  DECLARE_PROCESSOR(ByteBeats, bytebeats_);
#ifdef NUMBER_STATION
  DECLARE_PROCESSOR(NumberStation, number_station_);
#endif
  DECLARE_PROCESSOR(DualAttackEnvelope, dual_attack_envelope_);
  DECLARE_PROCESSOR(LoopingEnvelope, looping_envelope_);
  DECLARE_PROCESSOR(RepeatingAttackEnvelope, repeating_attack_envelope_);
  DECLARE_PROCESSOR(RandomisedEnvelope, randomised_envelope_);
  DECLARE_PROCESSOR(RandomisedBassDrum, randomised_bass_drum_);
  DECLARE_PROCESSOR(RandomisedSnareDrum, randomised_snare_drum_);
  DECLARE_PROCESSOR(TuringMachine, turing_machine_);
  DECLARE_PROCESSOR(ModSequencer, mod_sequencer_);
  DECLARE_PROCESSOR(FmLfo, fmlfo_);
  DECLARE_PROCESSOR(WsmLfo, wsmlfo_);
  DECLARE_PROCESSOR(Plo, plo_);

  DISALLOW_COPY_AND_ASSIGN(Processors);
};

extern Processors processors[2];

}  // namespace peaks

#endif  // PEAKS_PROCESSORS_H_
